starklicht/starklicht-stm32/Inc/main.h

#define LED1_Pin GPIO_PIN_13
#define LED1_GPIO_Port GPIOC
#define TEMP_LED_Pin GPIO_PIN_0
#define TEMP_LED_GPIO_Port GPIOA
#define TEMP_DR_Pin GPIO_PIN_1
#define TEMP_DR_GPIO_Port GPIOA
#define TEMP_DG_Pin GPIO_PIN_2
#define TEMP_DG_GPIO_Port GPIOA
#define TEMP_DB_Pin GPIO_PIN_3
#define TEMP_DB_GPIO_Port GPIOA
#define RED_Pin GPIO_PIN_4
#define RED_GPIO_Port GPIOA
#define GREEN_Pin GPIO_PIN_5
#define GREEN_GPIO_Port GPIOA
#define BLUE_Pin GPIO_PIN_6
#define BLUE_GPIO_Port GPIOA
#define MASTER_Pin GPIO_PIN_7
#define MASTER_GPIO_Port GPIOA
#define CURR_Pin GPIO_PIN_0
#define CURR_GPIO_Port GPIOB
#define BATTERY_VOLTAGE_Pin GPIO_PIN_1
#define BATTERY_VOLTAGE_GPIO_Port GPIOB
#define BT4_Pin GPIO_PIN_12
#define BT4_GPIO_Port GPIOB
#define BT3_Pin GPIO_PIN_13
#define BT3_GPIO_Port GPIOB
#define BT2_Pin GPIO_PIN_14
#define BT2_GPIO_Port GPIOB
#define BT1_Pin GPIO_PIN_15
#define BT1_GPIO_Port GPIOB
#define BT_STATE_Pin GPIO_PIN_8
#define BT_STATE_GPIO_Port GPIOA
#define CS_Pin GPIO_PIN_12
#define CS_GPIO_Port GPIOA
#define DC_Pin GPIO_PIN_15
#define DC_GPIO_Port GPIOA
#define RST_Pin GPIO_PIN_4
#define RST_GPIO_Port GPIOB
#define R_LED_Pin GPIO_PIN_6
#define R_LED_GPIO_Port GPIOB
#define G_LED_Pin GPIO_PIN_7
#define G_LED_GPIO_Port GPIOB
#define B_LED_Pin GPIO_PIN_8
#define B_LED_GPIO_Port GPIOB
#define PWM_LUEFTER_Pin GPIO_PIN_9
#define PWM_LUEFTER_GPIO_Port GPIOB
