starklicht/starklicht-stm32/Inc/starklicht_library/color.h

//
// Created by Jannis Jahr on 2019-12-14.
//
#ifndef ANIMATOR_COLOR_H
#define ANIMATOR_COLOR_H
#include "stdint.h"

struct Color
{
    uint16_t r;
    uint16_t g;
    uint16_t b;
    uint16_t master;
};

#endif // ANIMATOR_COLOR_H
